betrusted-io/betrusted-hardware/mainboard-evt2/trusted_io_evt2.pdf

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
D | D
C | C
B | B
A | A

## Title

Size | Number | | Revision

A

Date: | 6/10/2019 | Sheet | of
File: | F:\largework\..\00_map.SchDoc | Drawn By:

# Licensed under CERN OHL v1.2 or later

# Copyright 2019 Andrew "bunnie" Huang

# Betrusted - Mainboard

Power sequencing:

* START with all systems off.
* VBUS (external power) applied, both U and T domains power on, and cannot be powered off until VBUS is removed. However, devices can still go into a power-saving mode on their own.
* VBUS removed:
* T-domain only powers down when both CPU and UP5K approve it. Normally, UP5K should cut its override once the CPU is confirmed to boot, so effectively the CPU has sef-control for power down.
* U-domain can self-power down whenever, but normally it's meant to be always-on. It powers off only when the battery reaches 0% to protect the battery. U-domain manages all charge and gas gauge hardware, and reports status to T-domain via COM SPI interface.
* It is up to the T-domain to monitor power via firmware COM SPI interface to UP5K to coordinate on the 0% power down. UP5K can trigger an interrupt in case of emergency, but T domain retains full authority to ignore it.
* Once U-domain is powered down, CPU can power on with T_TO_U_ON. This is useful in case RTC wakes up FPGA and it needs to also wake up the UP5K.

The nominal power strategy is power-on boot, and after a certain time-out interval of no activity, the FPGA will power itself down completely, and rely on the U-domain to monitor wake-up keys to power the FPGA domain up, or a callback can be set for a wake-up at no later than a specified timeout.

* U-domain can activate keyboard backlights to give instant UX response to monitor key press.
* T-domain can deny U-domain monitoring of keys via hardware signal, to avoid information leakage between the two domains.
* T-domain controls the LCD backlight, if present.
* After a T-domain power-down, the U-domain has the option to discharge the voltage rails with FPGA_DIS. This is provisioned to guarantee power sequencing is met even if the FPGA power down is very brief.

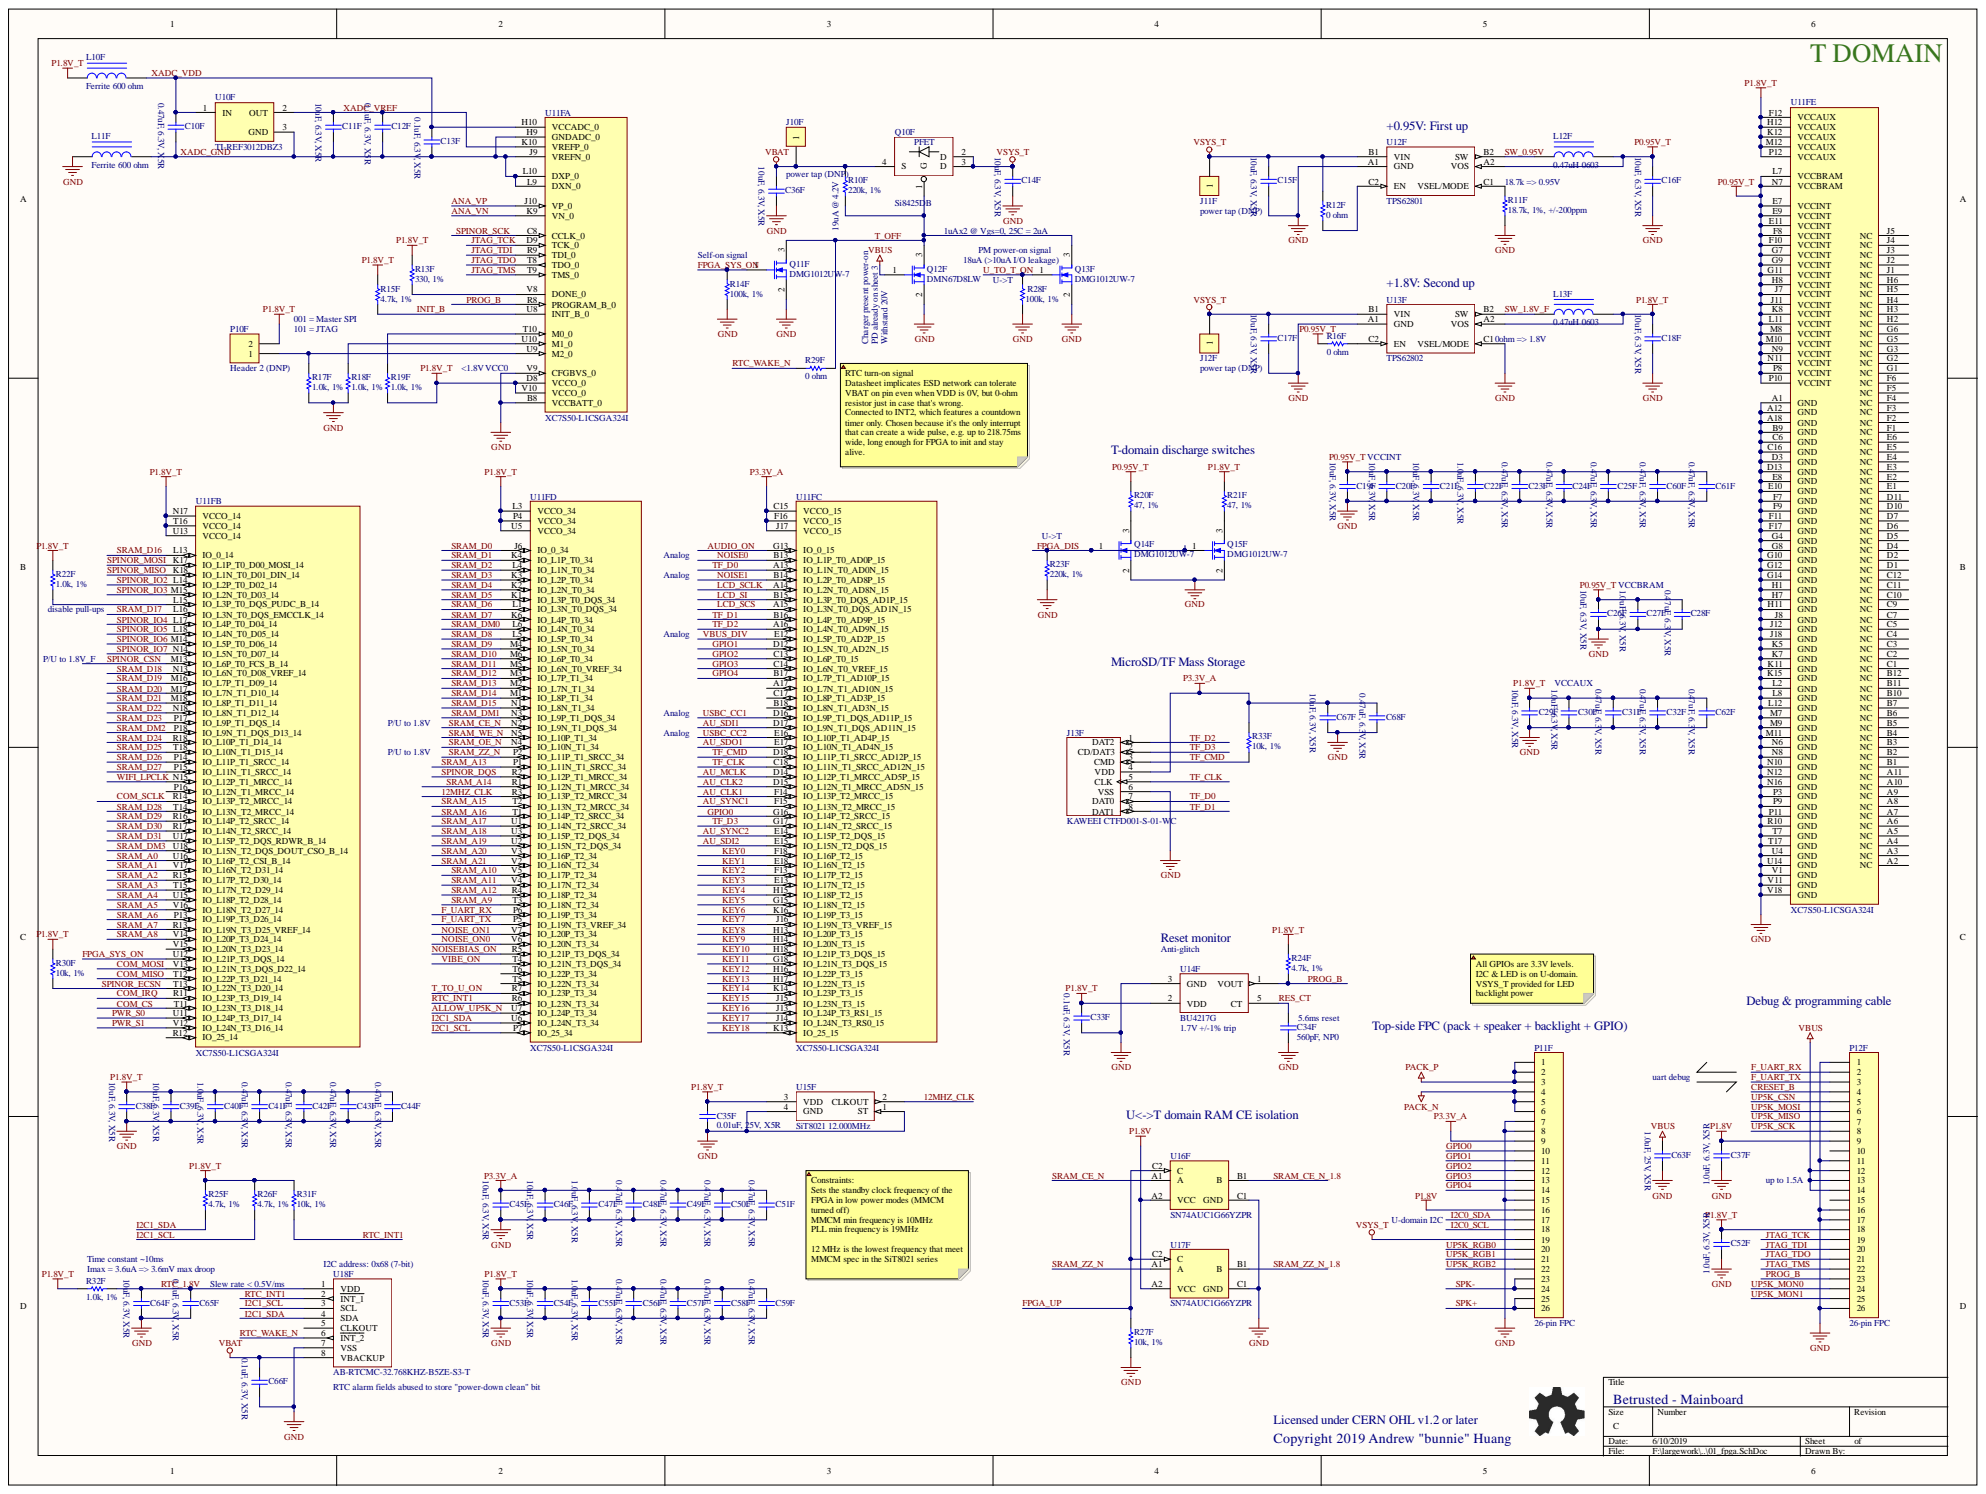
[picture p29: page 2]

Charger present power-on

PD already on sheet 3

RTC turn-on signal
Datasheet implicates ESD network can tolerate
VBAT on pin even when VDD is 0V, but 0-ohm
resistor just in case that's wrong.
Connected to INT2, which features a countdown
timer only. Chosen because it's the only interrupt
that can create a wide pulse, e.g. up to 218.75ms
wide, long enough for FPGA to init and stay
alive.

MicroSD/TF Mass Storage

Reset monitor Anti-glitch

All GPIOs are 3.3V levels.
I2C & LED is on U-domain.
VSYS_T provided for LED
backlight power

Top-side FPC (pack + speaker + backlight + GPIO)

U<->T domain RAM CE isolation

Constraints:
Sets the standby clock frequency of the
FPGA in low power modes (MMCM
turned off)
MMCM min frequency is 10MHz
PLL min frequency is 19MHz

12 MHz is the lowest frequency that meet
MMCM spec in the SiT8021 series

AB-RTCMC-32.768KHZ-B5ZE-S3-T
RTC alarm fields abused to store "power-down clean" bit

Licensed under CERN OHL v1.2 or later
Copyright 2019 Andrew "bunnie" Huang

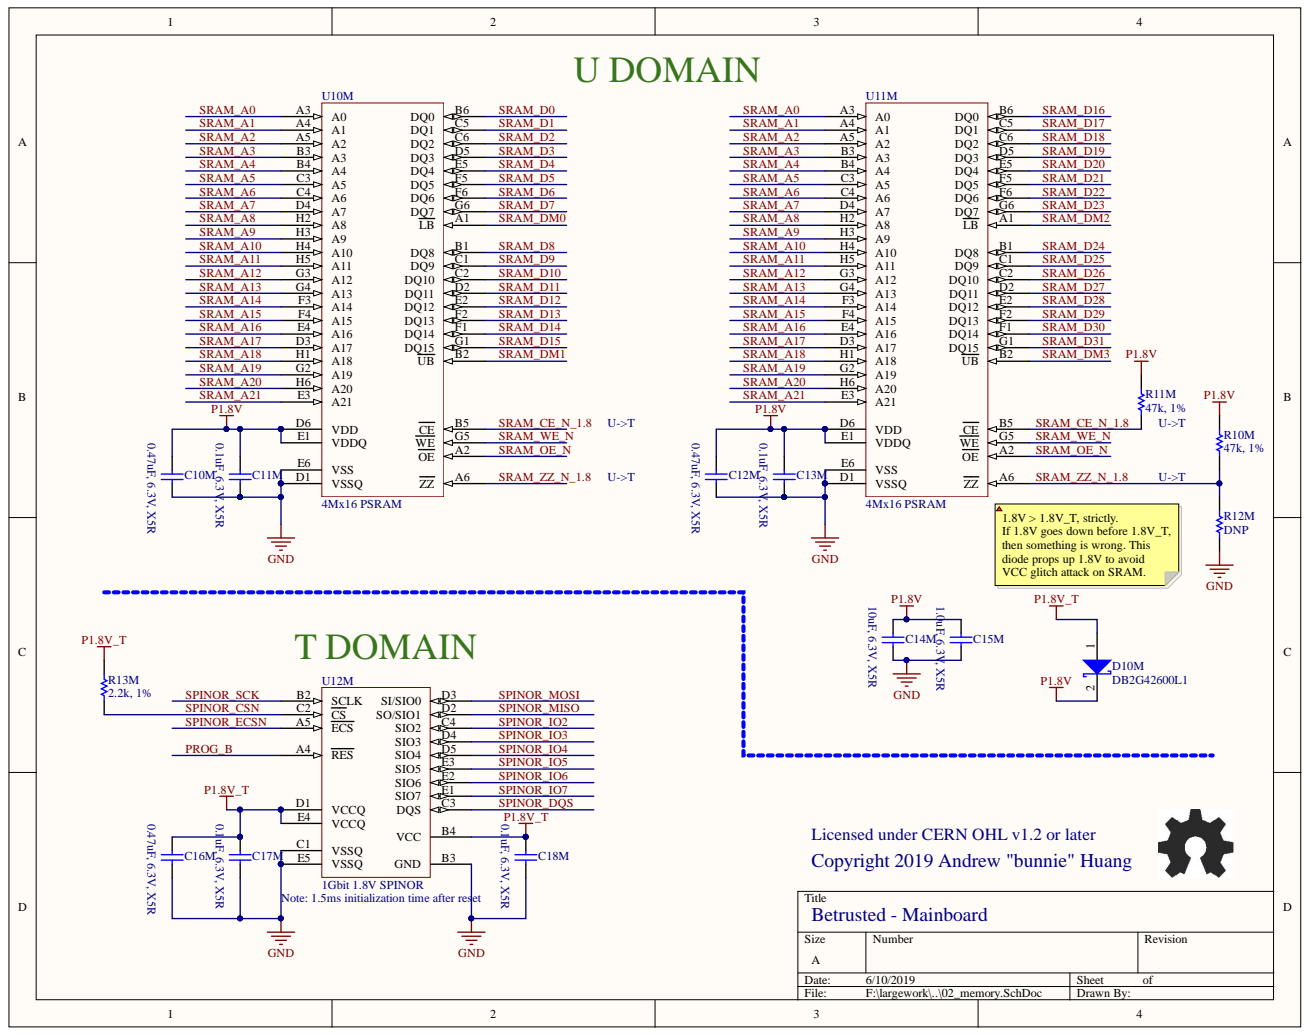
[picture p30: page 3]

Licensed under CERN
Copyright 2019 Andrew "bunnie" Huang

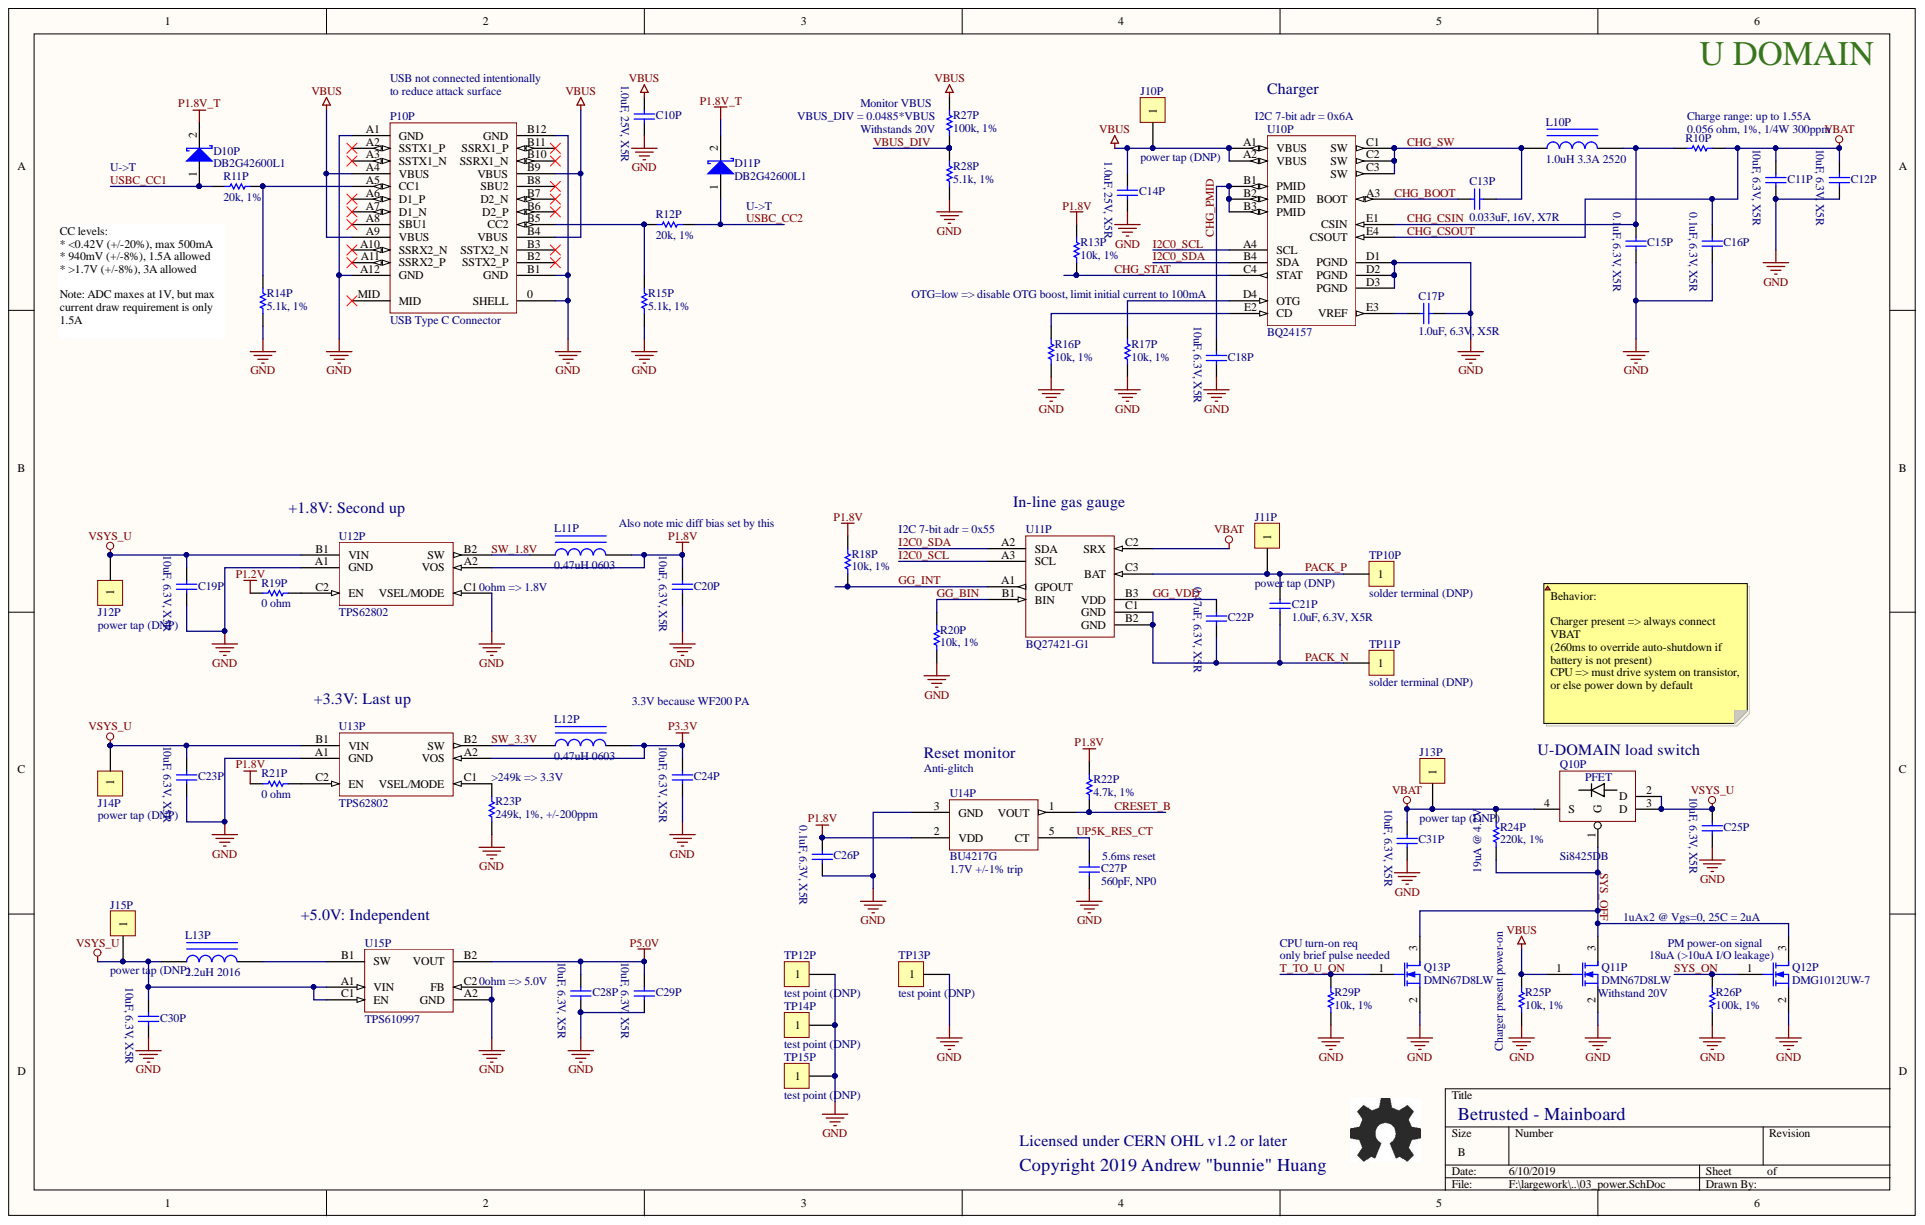
[picture p31: page 4]

USB not connected intentionally
to reduce attack surface

Charge range: up to 1.55A

Note: ADC maxes at 1V, but max
current draw requirement is only

OTG=low => disable OTG boost, limit initial current to 100mA

B | C18P solder terminal (DNP) | B

In-line gas gauge

Also note mic diff bias set by this

P1.2V 0 ohm | | EN C2 | L12P

BIN B1

Charger present => always connect
VBAT
(260ms to override auto-shutdown if
battery is not present)
CPU => must drive system on transistor,
or else power down by default

P1.8V 0 ohm | EN C2

PFET

power tap (DNP)

CPU turn-on req
only brief pulse needed

Charger present power-on

Licensed under CERN OHL v1.2 or later
Copyright 2019 Andrew "bunnie" Huang

Date: 6/10/2019 | Sheet of
File: F:\largework\..\03_power.SchDoc | Drawn By:

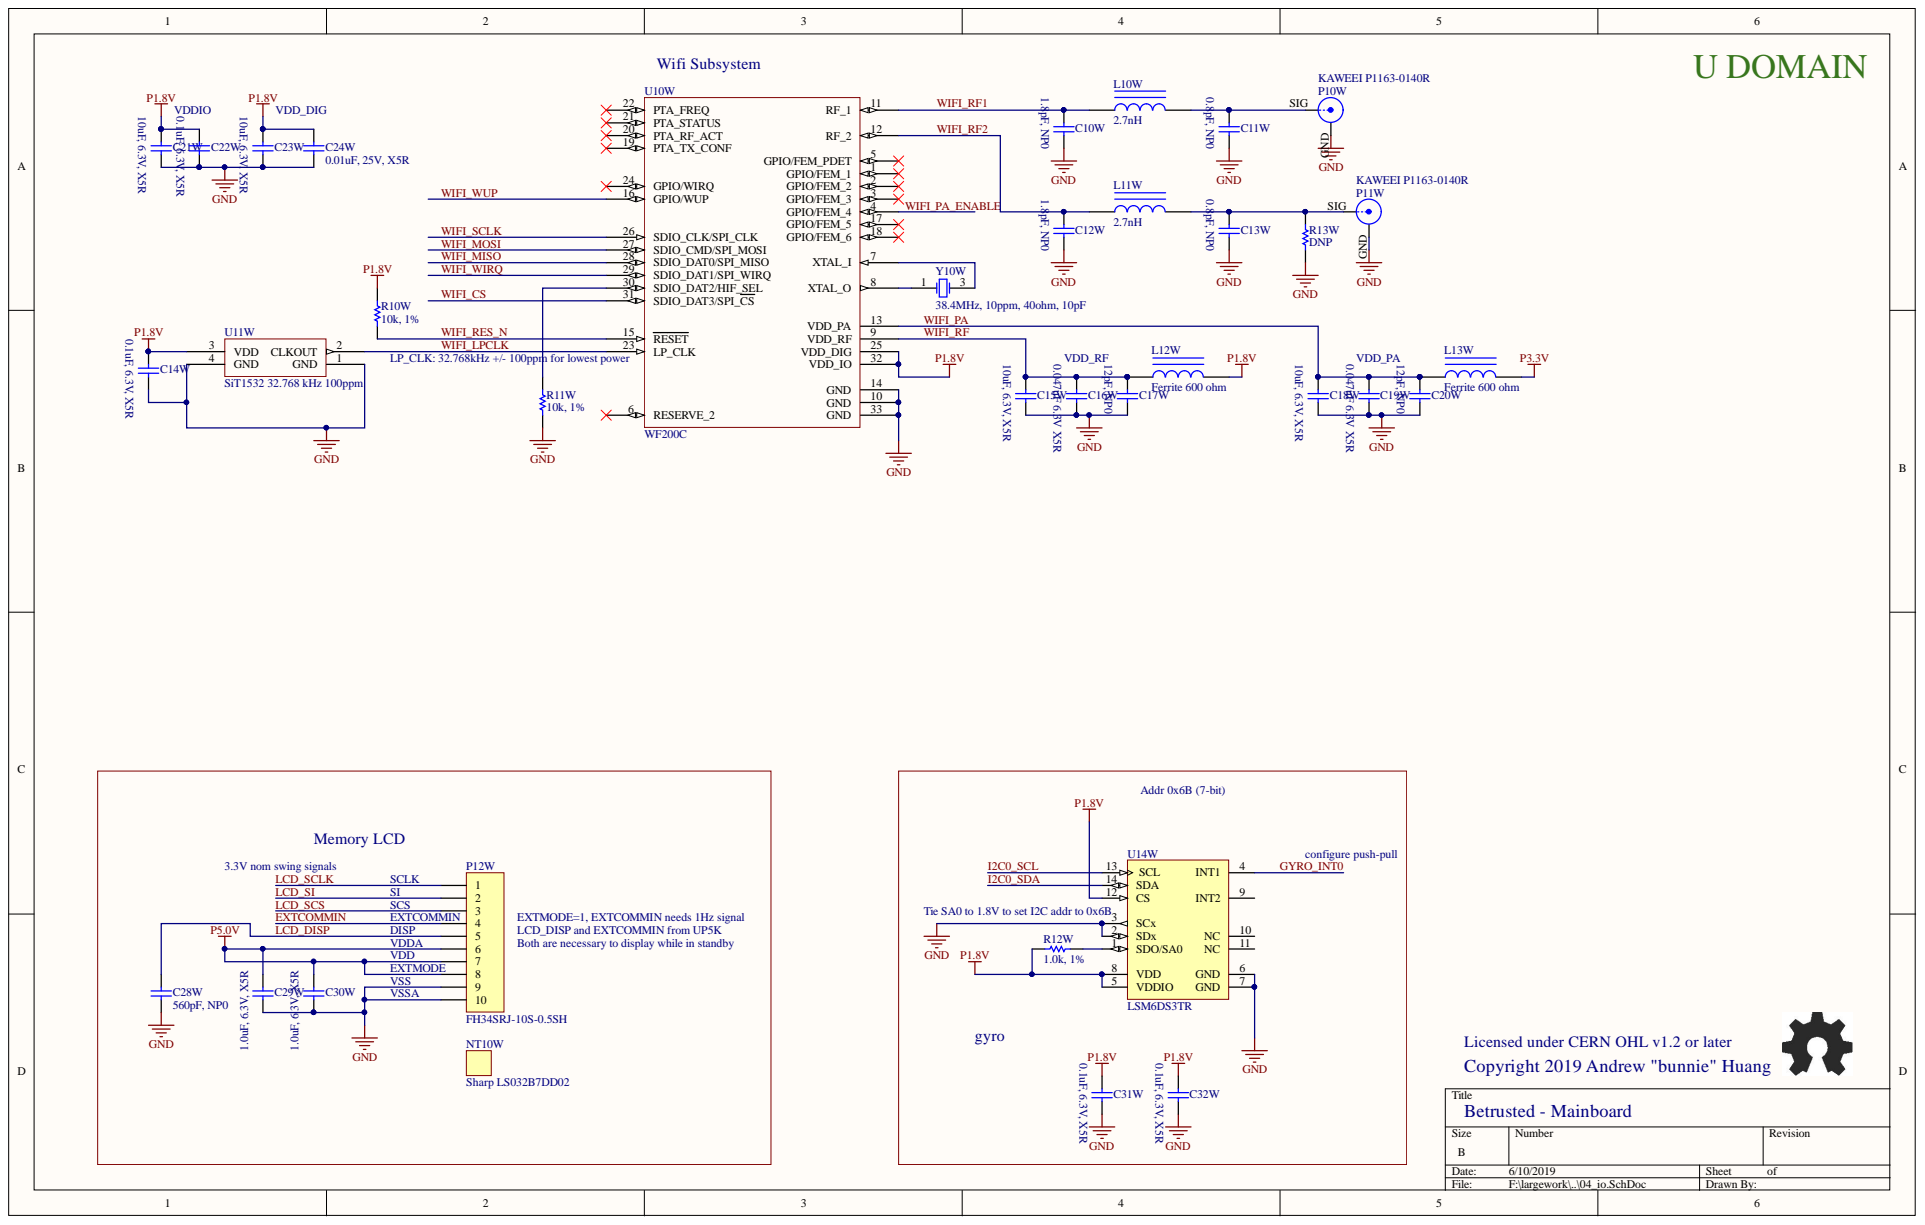
[picture p32: page 5]

Tie SA0 to 1.8V to set I2C addr to 0x6B

EXTMODE=1, EXTCOMMIN needs 1Hz signal
LCD_DISP and EXTCOMMIN from UP5K

VDD
EXTMODE
VSS

Licensed under CERN OHL v1.2 or later
Copyright 2019 Andrew "bunnie" Huang

Size B | Number | Revision

Date: 6/10/2019 | Sheet of
File: F:\largework\..\04_io.SchDoc | Drawn By:

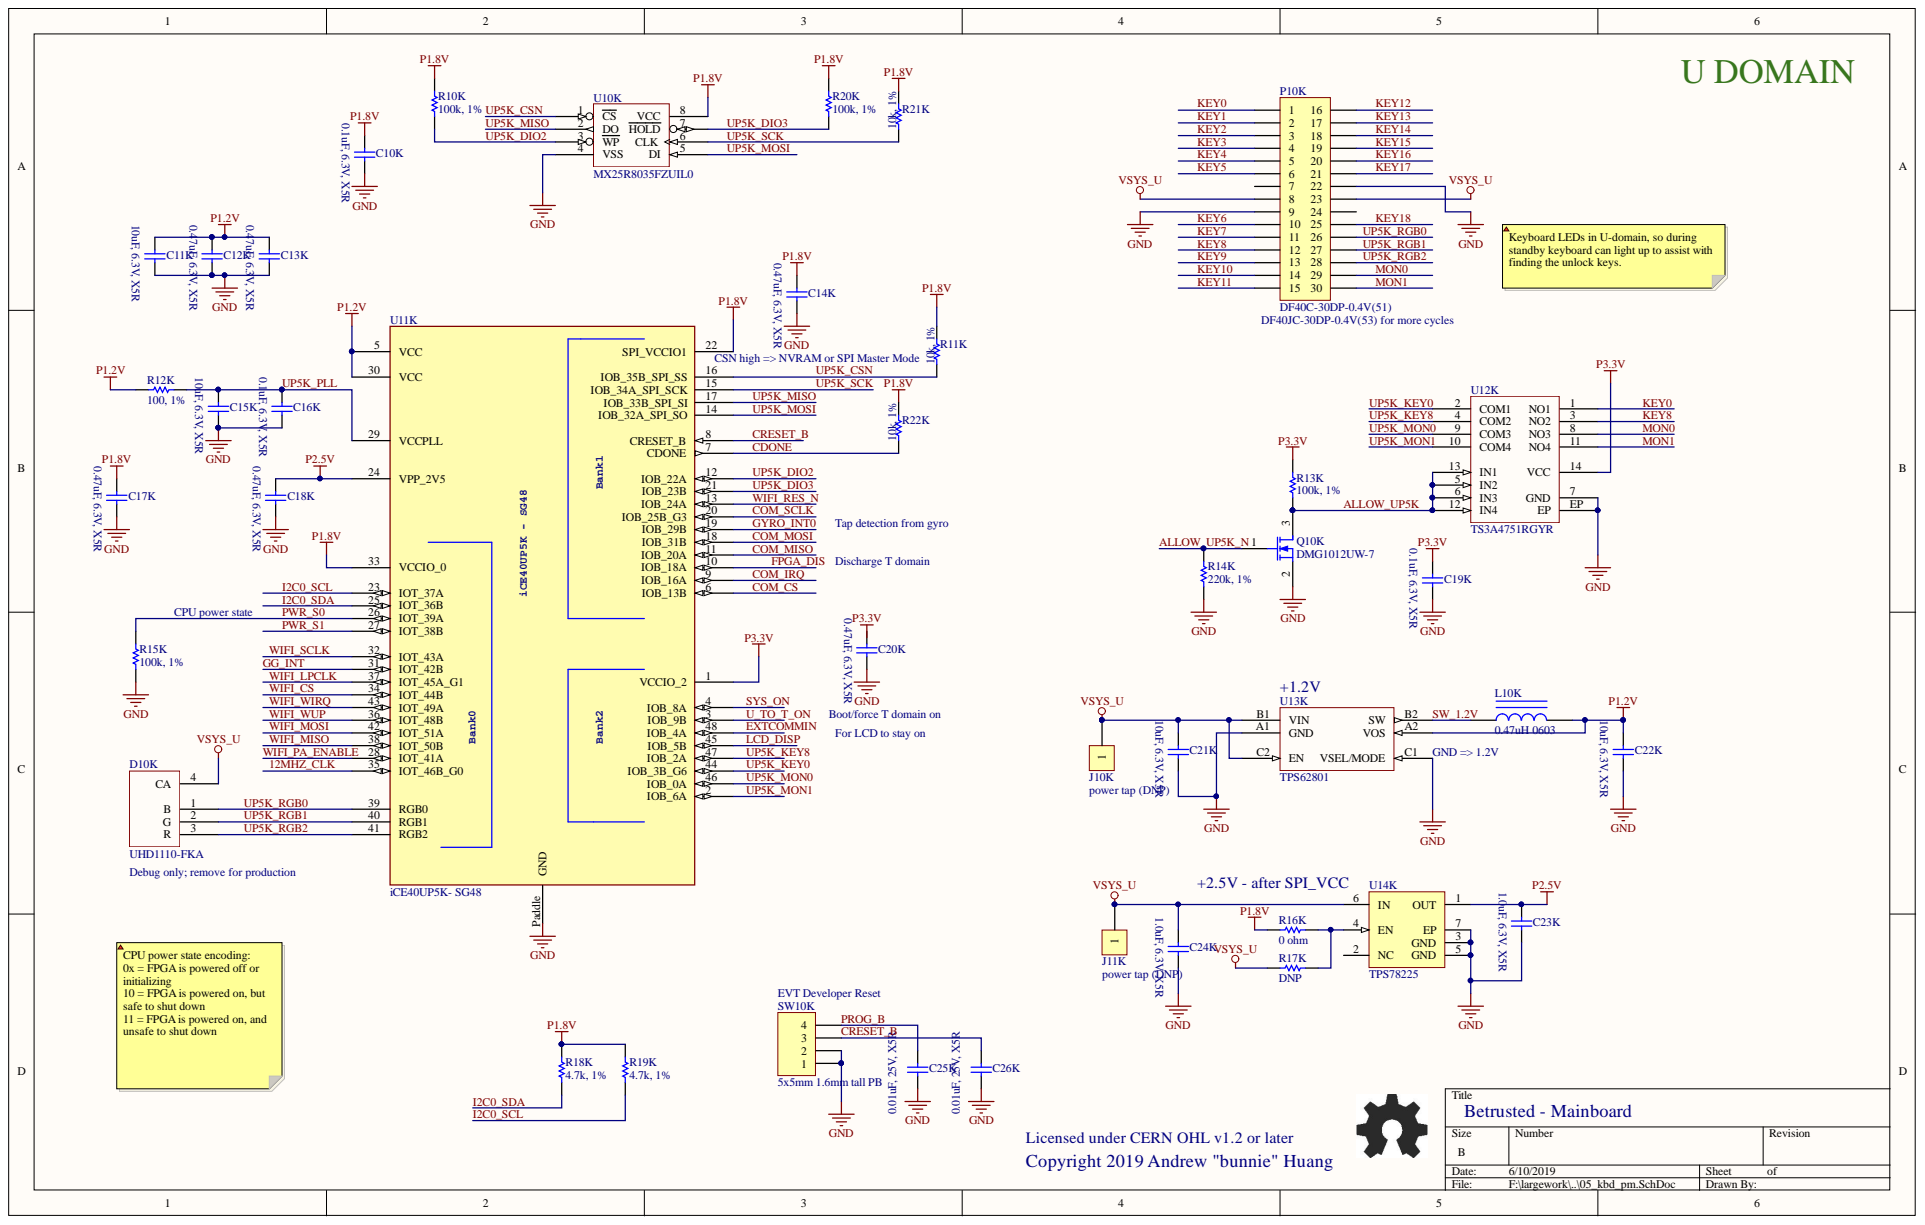
[picture p33: page 6]

Keyboard LEDs in U-domain, so during
standby keyboard can light up to assist with
finding the unlock keys.

CSN high => NVRAM or SPI Master Mode

Tap detection from gyro

Boot/force T domain on
For LCD to stay on

UHD1110-FKA
Debug only; remove for production

CPU power state encoding:
0x = FPGA is powered off or
initializing
10 = FPGA is powered on, but
safe to shut down
11 = FPGA is powered on, and
unsafe to shut down

Licensed under CERN OHL v1.2 or later
Copyright 2019 Andrew "bunnie" Huang

Date: 6/10/2019 | Sheet of
File: F:\largework\..\05_kbd_pm.SchDoc | Drawn By:

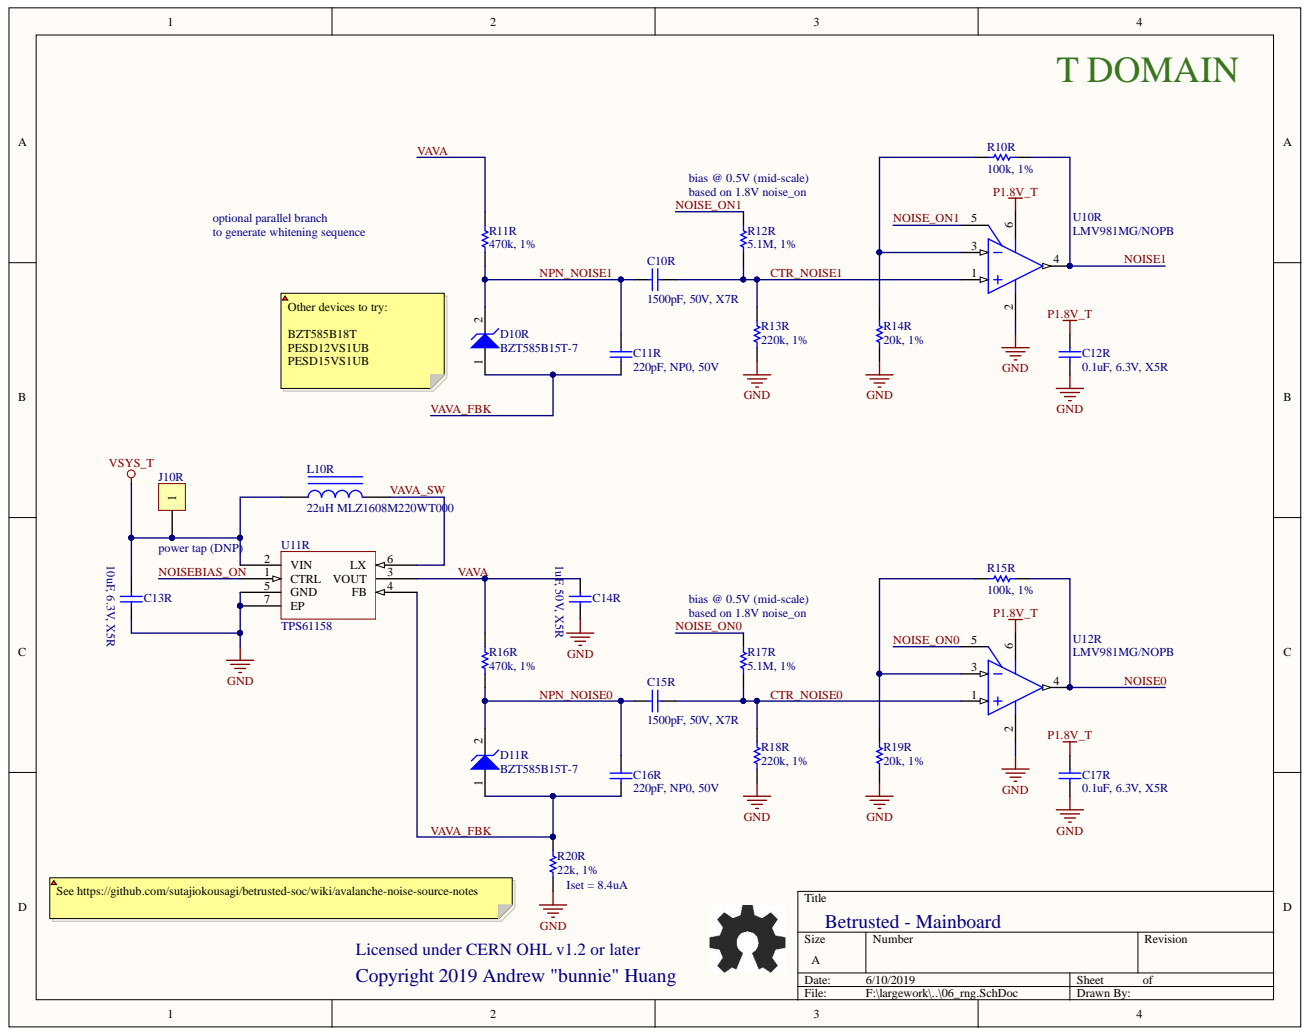
[picture p34: page 7]

optional parallel branch
to generate whitening sequence

Other devices to try:

See https://github.com/sutajiokousagi/betrusted-soc/wiki/avalanche-noise-source-notes

Licensed under CERN OHL v1.2 or later
Copyright 2019 Andrew "bunnie" Huang

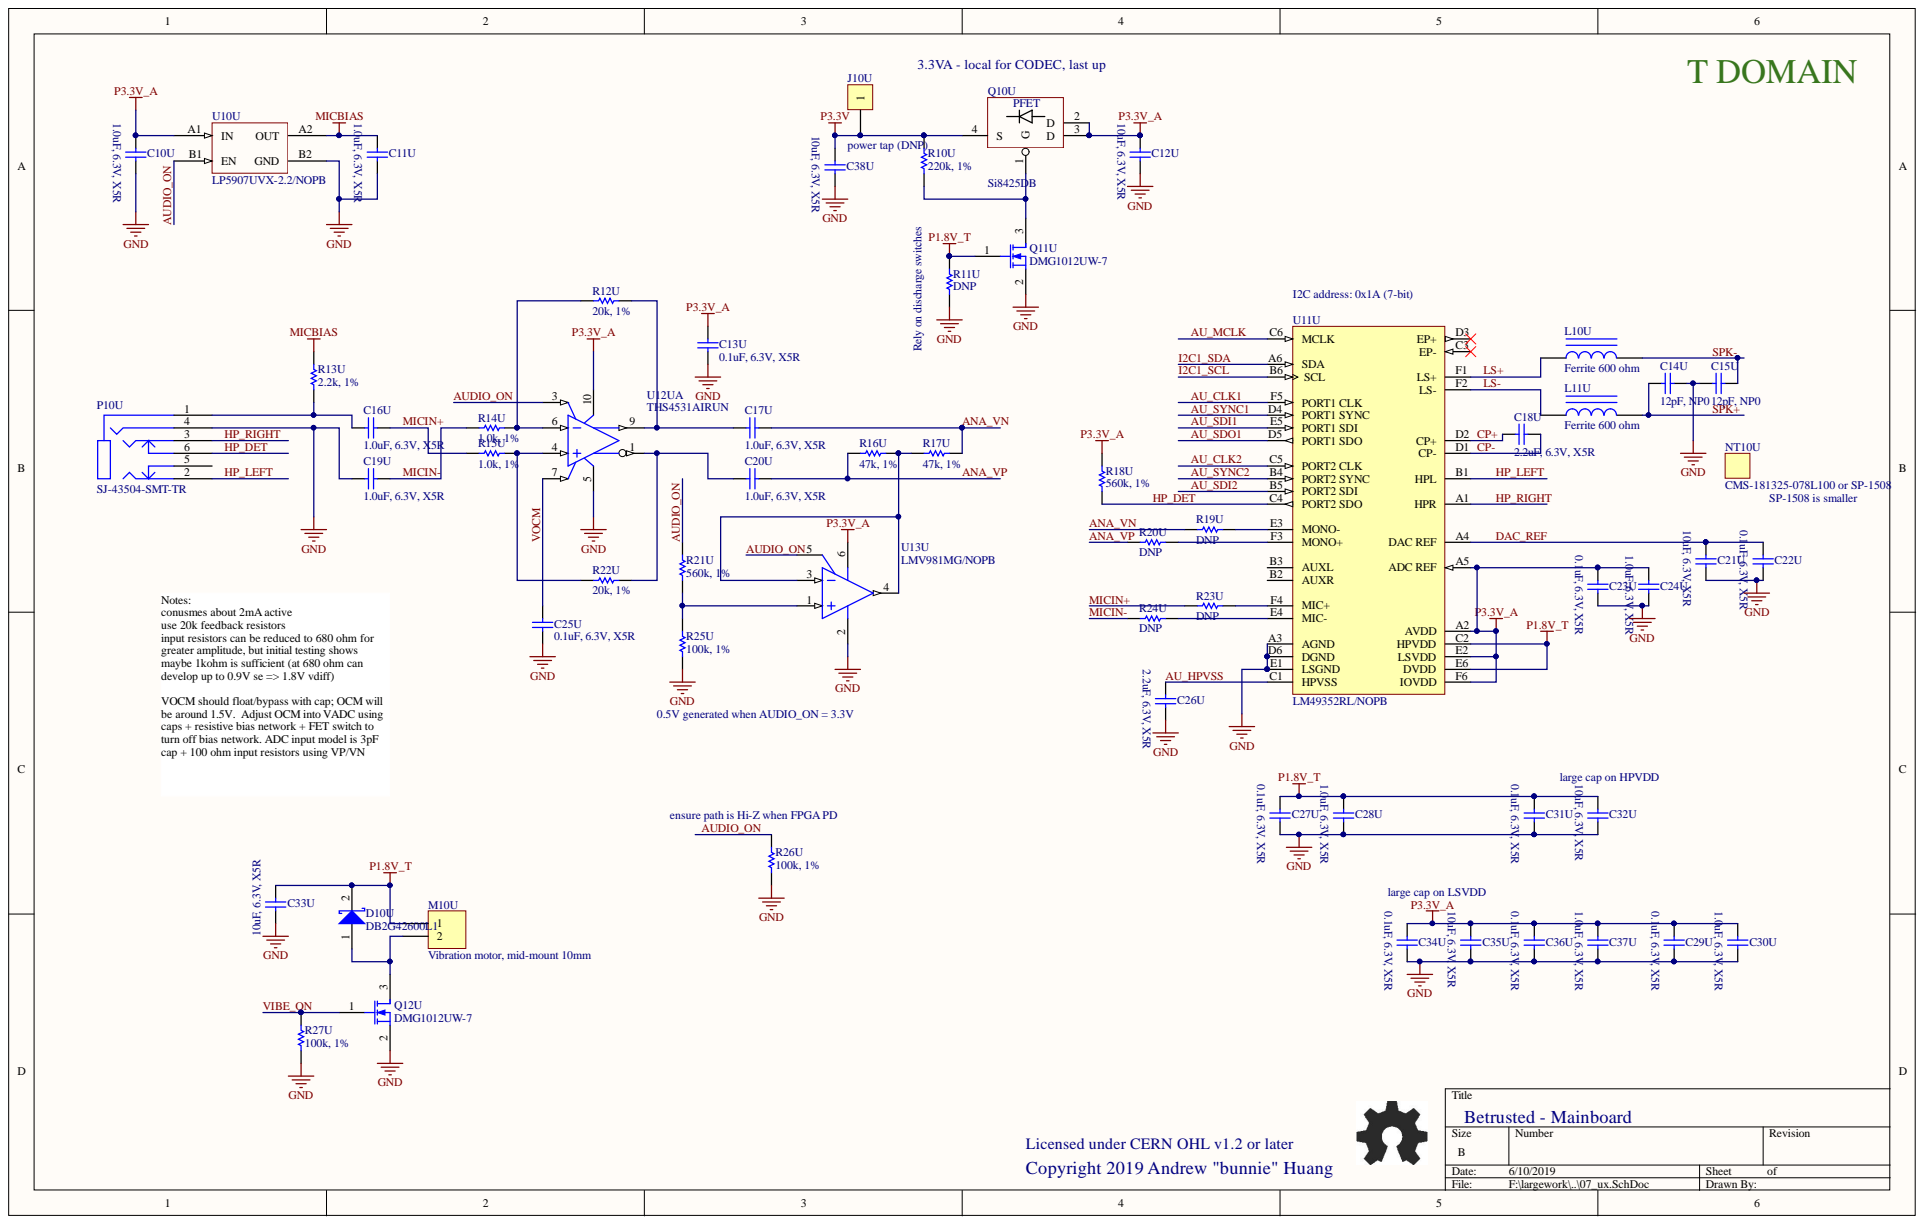
[picture p35: page 8]

3.3VA - local for CODEC, last up

PFET

10uF, 6.3V, X5R GND
GND Rely on discharge switches

power tap (DNP)

Notes:
conusmes about 2mA active
use 20k feedback resistors
input resistors can be reduced to 680 ohm for
greater amplitude, but initial testing shows
maybe 1kohm is sufficient (at 680 ohm can
develop up to 0.9V se => 1.8V vdiff)

VOCM should float/bypass with cap; OCM will
be around 1.5V. Adjust OCM into VADC using
caps + resistive bias network + FET switch to
turn off bias network. ADC input model is 3pF
cap + 100 ohm input resistors using VP/VN

large cap on HPVDD

ensure path is Hi-Z when FPGA PD
AUDIO_ON

large cap on LSVDD

D10U
DB2G42600L1

Licensed under CERN OHL v1.2 or later
Copyright 2019 Andrew "bunnie" Huang

Size B | Number | Revision

Date: 6/10/2019 | Sheet of
File: F:\largework\..\07_ux.SchDoc | Drawn By:
