betrusted-io/betrusted-hardware/kbd-v3/pcb/betrusted-kbd-v3.pdf

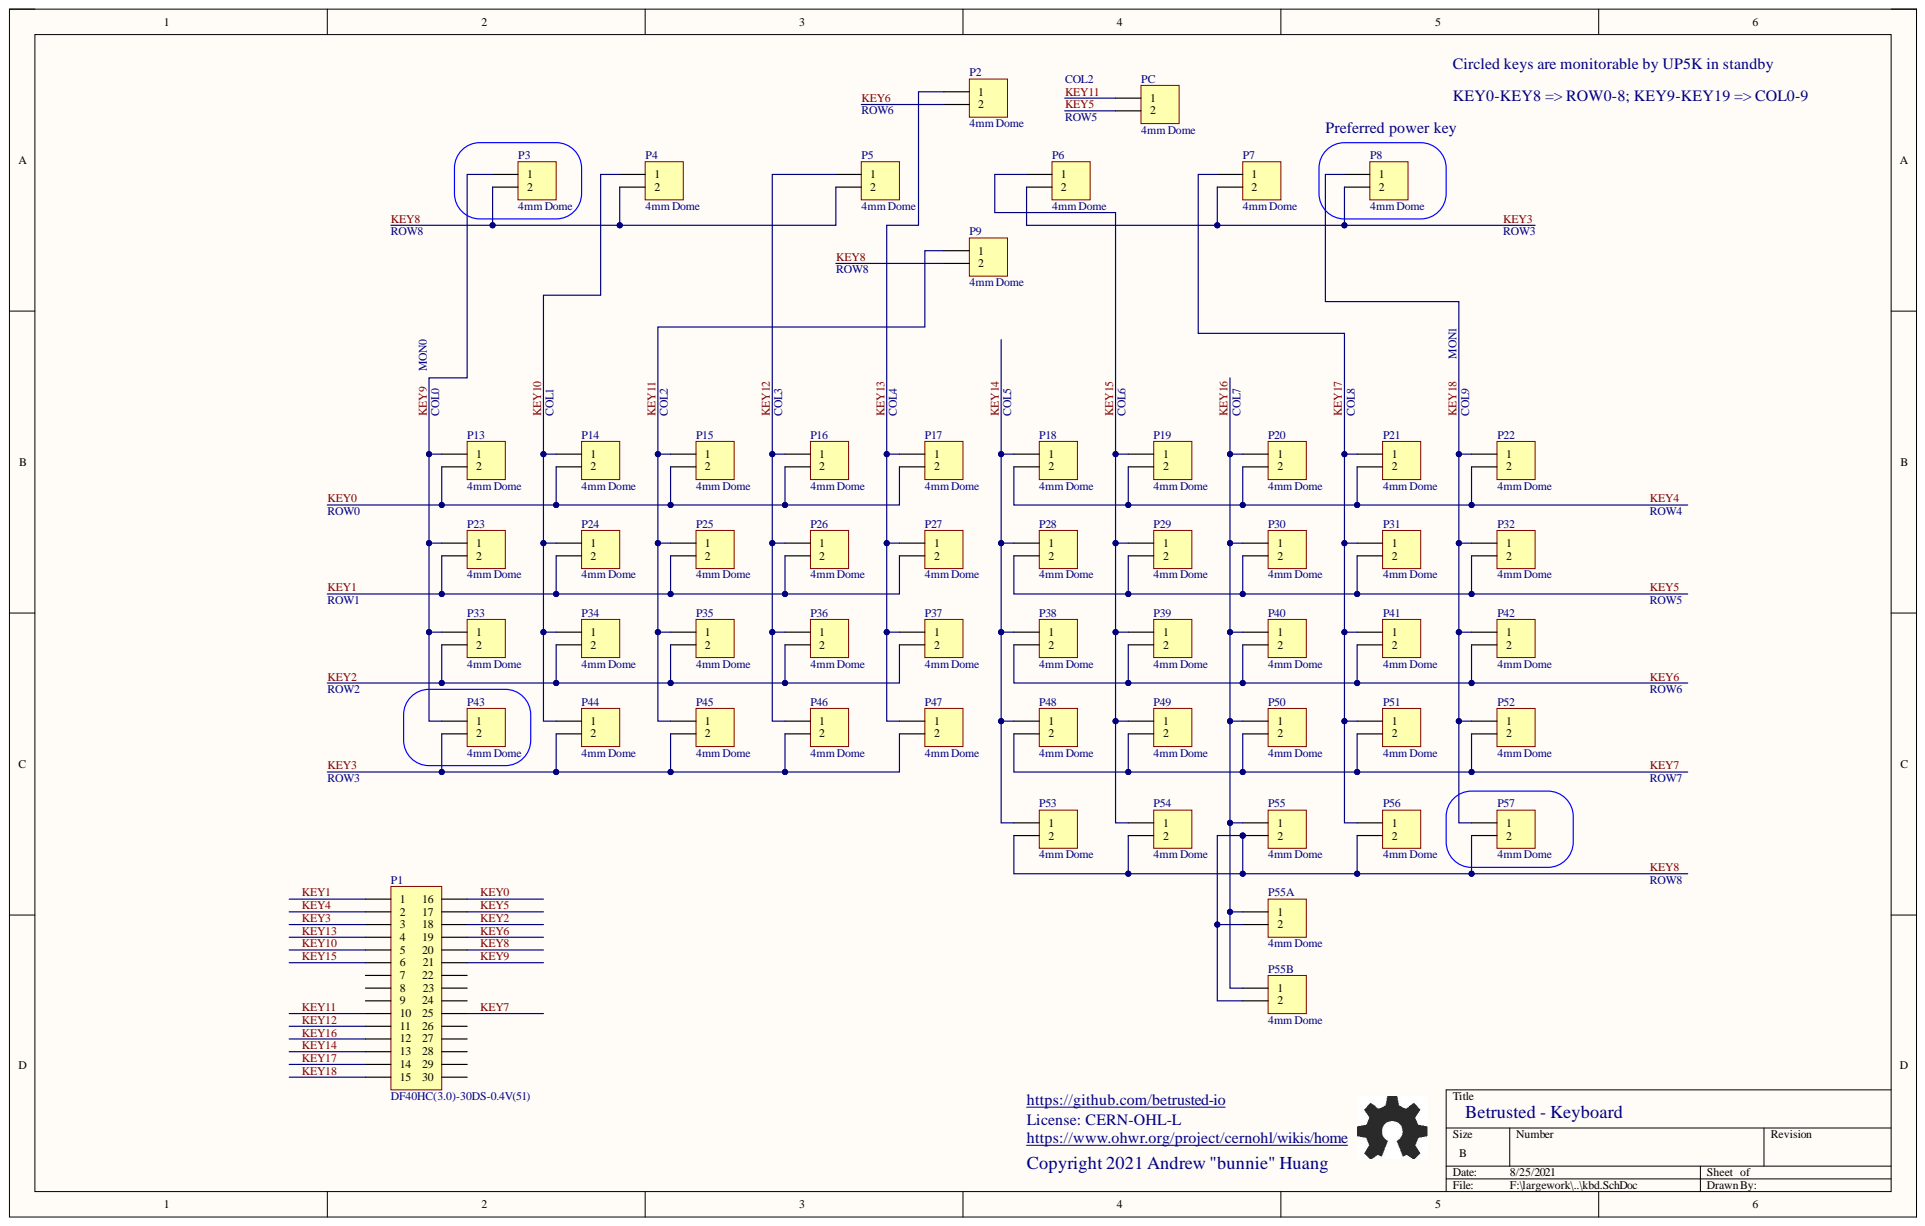
[picture p54: page 1]

MON1 Circled keys are monitorable by UP5K in standby

https://github.com/betrusted-io
License: CERN-OHL-L
https://www.ohwr.org/project/cernohl/wikis/home
Copyright 2021 Andrew "bunnie" Huang

Size B | Number | Revision

Date: 8/25/2021 | Sheet of
File: F:\largework\..\kbd.SchDoc | Drawn By:
