betrusted-io/betrusted-hardware/case-v1/betrusted-dvt1-fpc-dims.PDF

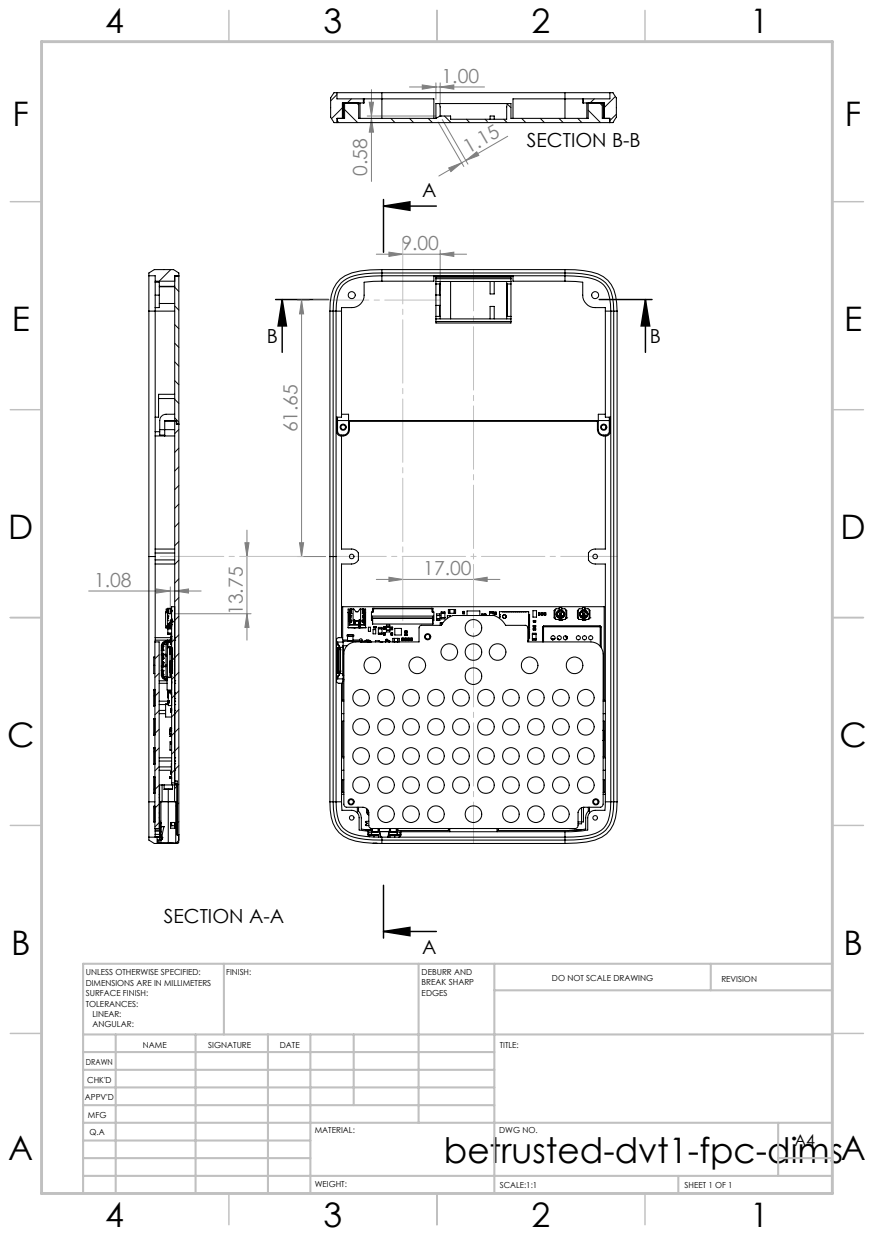
[picture p55: page 1]
SECTION A-A; SECTION B-B; FINISH:; DEBURR AND; BREAK SHARP; DO NOT SCALE DRAWING; REVISION; SCALE:1:1; SHEET 1 OF 1

UNLESS OTHERWISE SPECIFIED:
DIMENSIONS ARE IN MILLIMETERS
SURFACE FINISH:
TOLERANCES:
LINEAR:
ANGULAR:

NAME | SIGNATURE | DATE | | | | TITLE:

DRAWN
CHK'D
APPV'D
MFG
Q.A | | | | MATERIAL: | DWG NO. | A4

betrusted-dvt1-fpc-dims
