betrusted-io/betrusted-hardware/case-v1/t-domain-shield.PDF

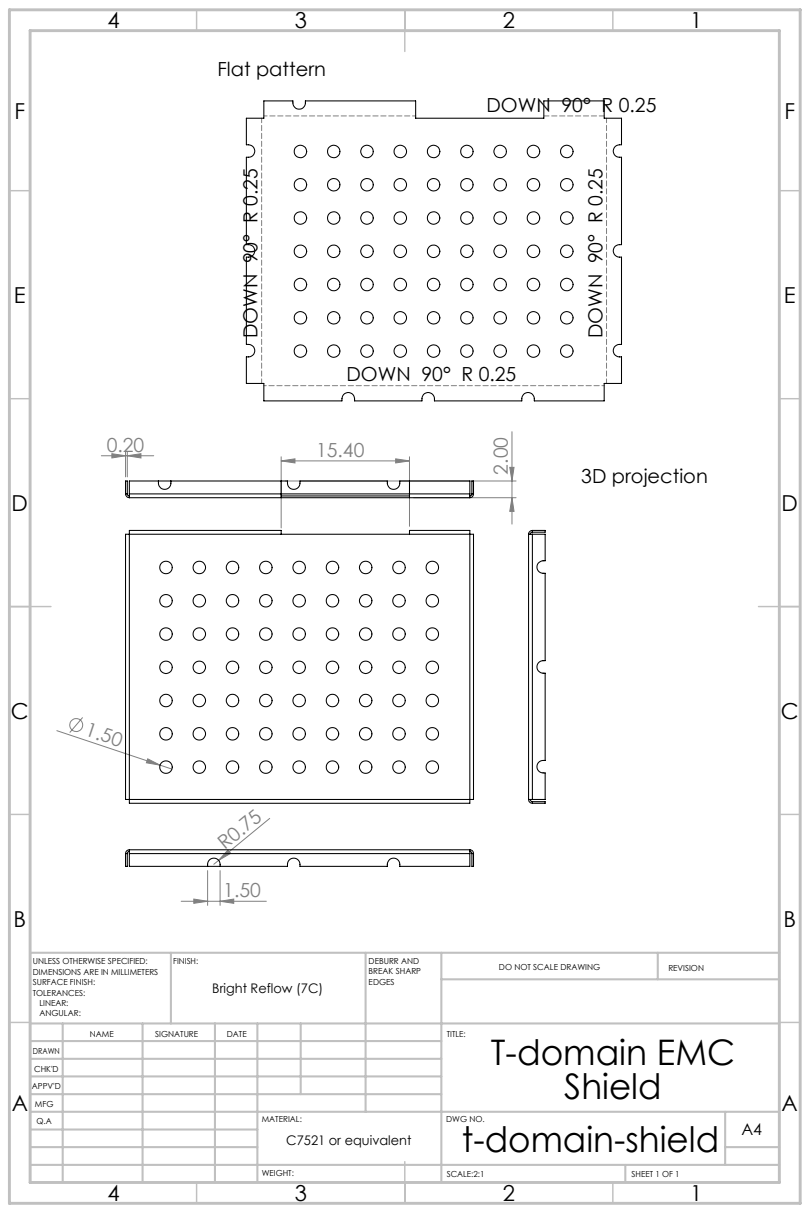
[picture p56: page 1]
DOWN 90° R 0.25; 3D projection; FINISH:; DEBURR AND; BREAK SHARP; DO NOT SCALE DRAWING; REVISION; SCALE:2:1; SHEET 1 OF 1; Bright Reflow (7C)

Flat pattern | DOWN 90° R 0.25

UNLESS OTHERWISE SPECIFIED:
DIMENSIONS ARE IN MILLIMETERS
SURFACE FINISH:
TOLERANCES:
LINEAR:
ANGULAR:

NAME | SIGNATURE | DATE | | | | TITLE: T-domain EMC Shield

DRAWN
CHK'D
APPV'D
MFG
Q.A | | | | MATERIAL: | DWG NO. t-domain-shield | A4 C7521 or equivalent
