betrusted-io/betrusted-hardware/case-v1/fab/bottom-case.PDF

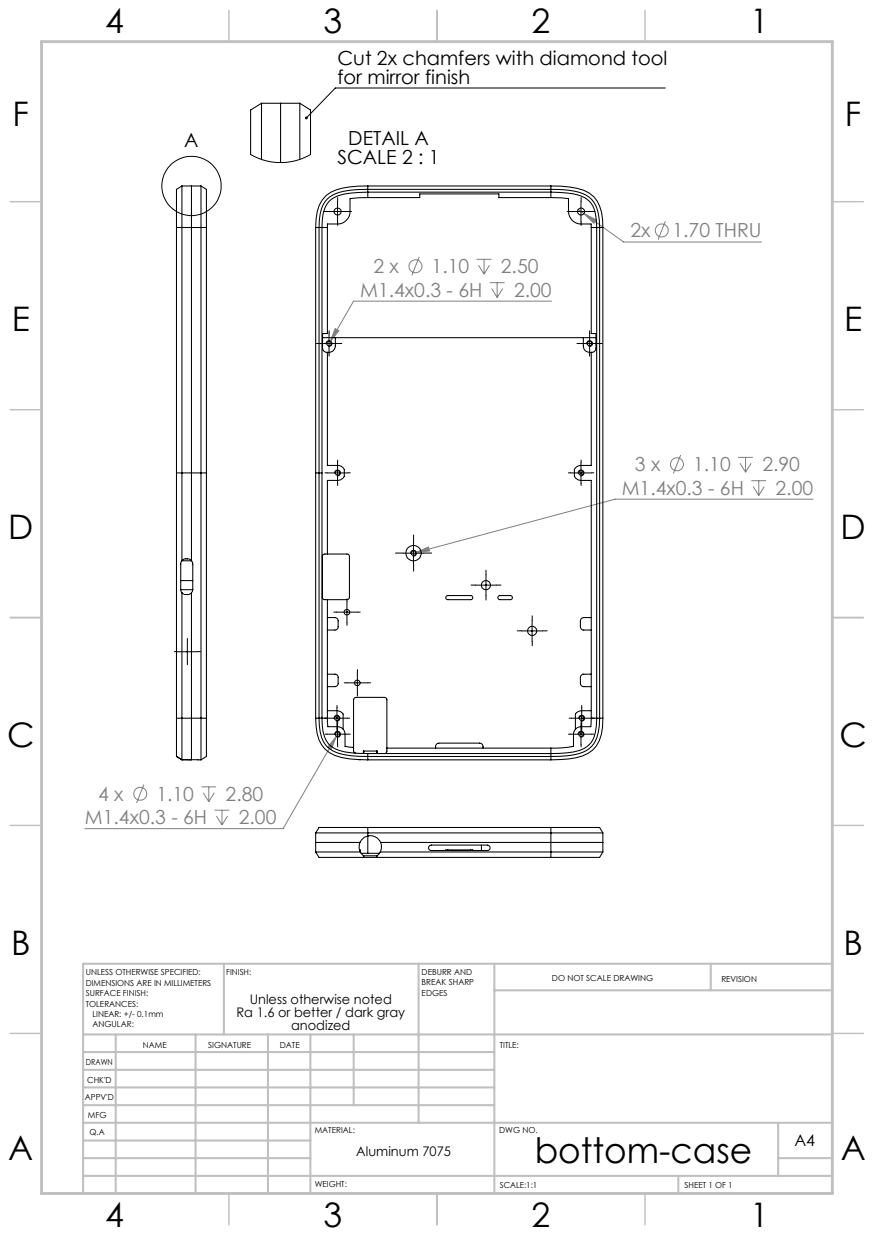
[picture p57: page 1]
2x 1.70 THRU; DETAIL A; SCALE 2 : 1; FINISH:; DEBURR AND; BREAK SHARP; DO NOT SCALE DRAWING; REVISION; SCALE:1:1; SHEET 1 OF 1

Cut 2x chamfers with diamond tool
for mirror finish

UNLESS OTHERWISE SPECIFIED:
DIMENSIONS ARE IN MILLIMETERS
SURFACE FINISH:
TOLERANCES:
LINEAR: +/- 0.1mm
ANGULAR:

Unless otherwise noted
Ra 1.6 or better / dark gray
anodized

NAME | SIGNATURE | DATE | | | | TITLE:

DRAWN
CHK'D
APPV'D
MFG
Q.A | | | | MATERIAL: | DWG NO. bottom-case | A4 Aluminum 7075
