betrusted-io/betrusted-hardware/case-v1/fab/radome.PDF

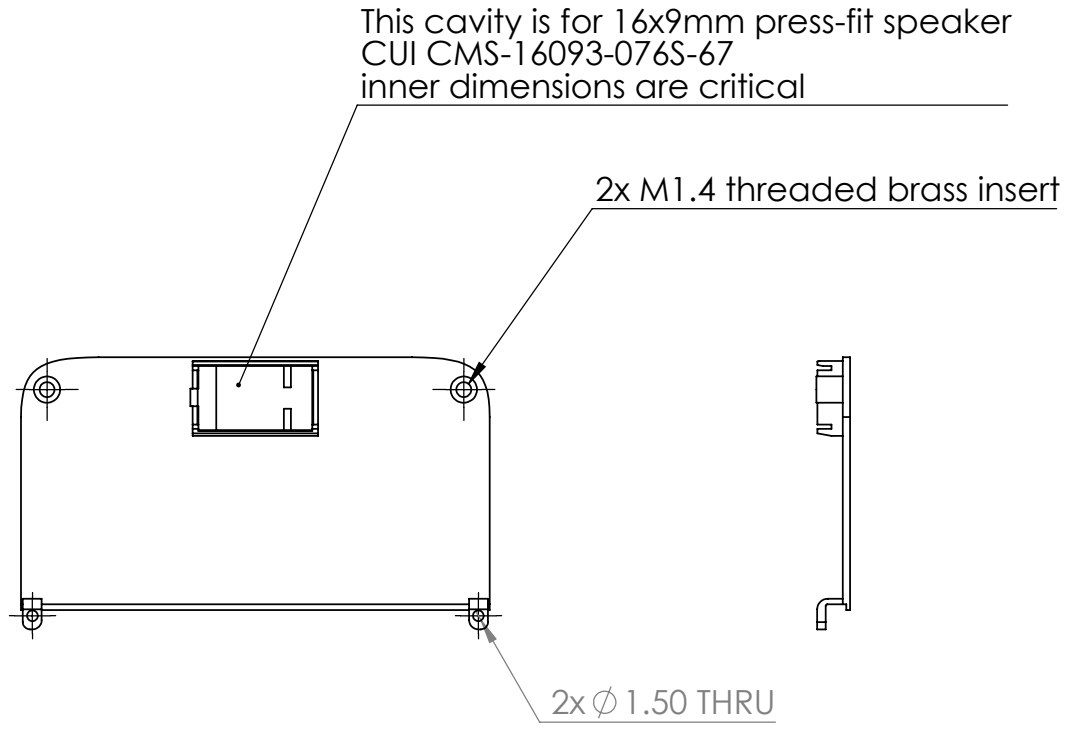
[picture p58: page 1]
2x 1.50 THRU; FINISH:; DEBURR AND; BREAK SHARP; DO NOT SCALE DRAWING; REVISION; SCALE:1:1; SHEET 1 OF 1

This cavity is for 16x9mm press-fit speaker
CUI CMS-16093-076S-67
inner dimensions are critical

2x M1.4 threaded brass insert

UNLESS OTHERWISE SPECIFIED:
DIMENSIONS ARE IN MILLIMETERS
SURFACE FINISH:
TOLERANCES:
LINEAR:
ANGULAR:

Fine satin black

NAME | SIGNATURE | DATE | | | | TITLE:

DRAWN
CHK'D
APPV'D
MFG
Q.A | | | | MATERIAL: ABS/PC | DWG NO. radome | A4
