betrusted-io/betrusted-hardware/rpi-hat-v3/Assembly Drawings.pdf

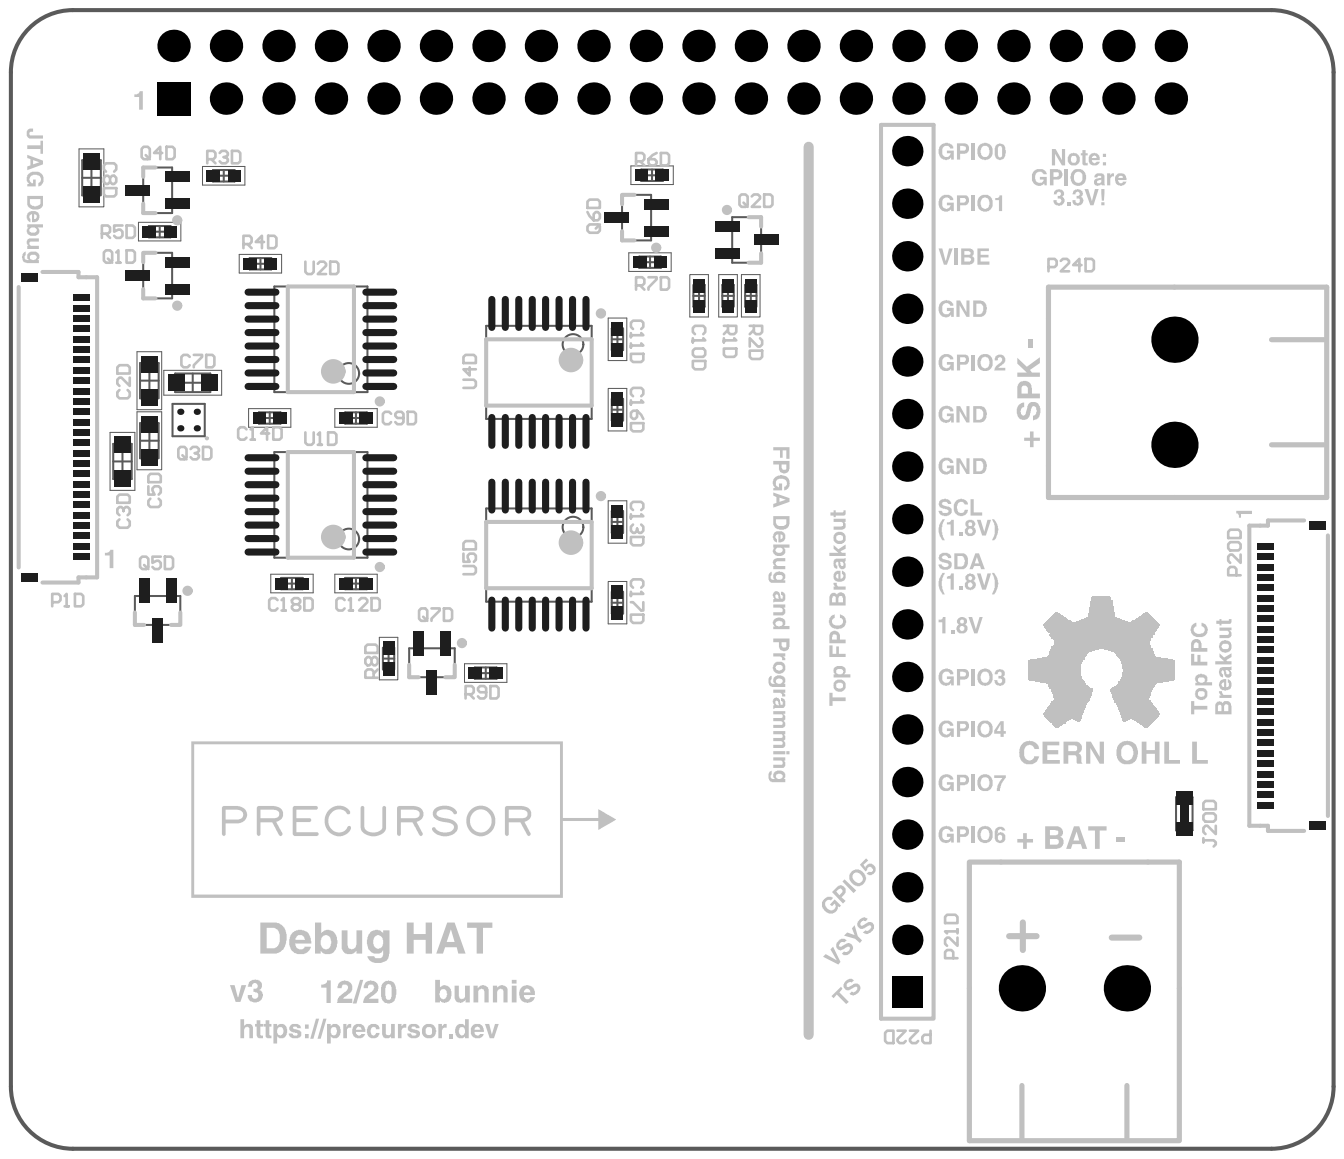
[picture p59: page 1]

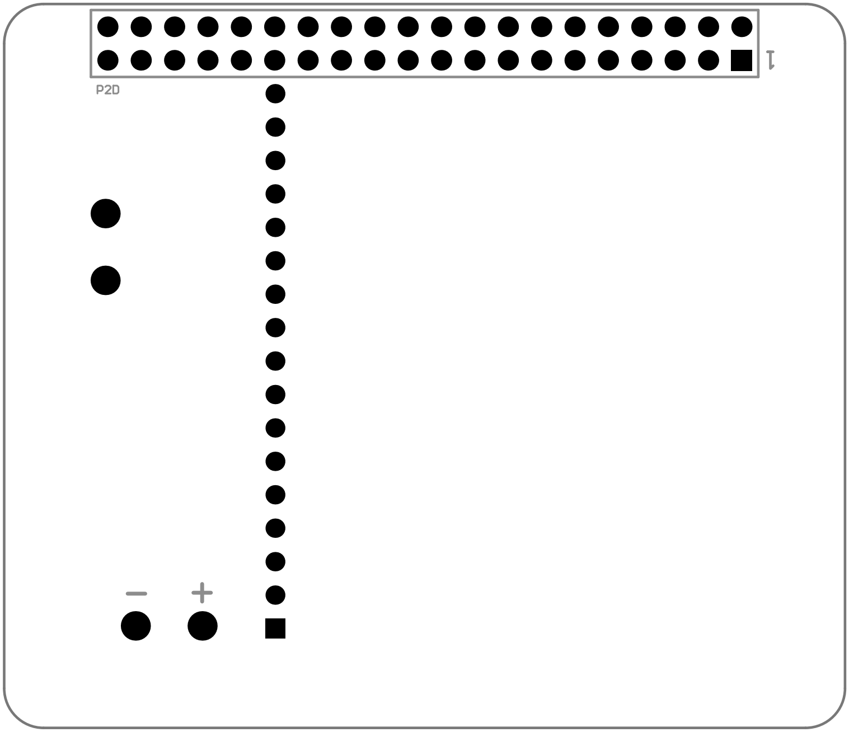
[picture p60: figure]
