betrusted-io/betrusted-hardware/case-v1/dvt1-test-mb.PDF

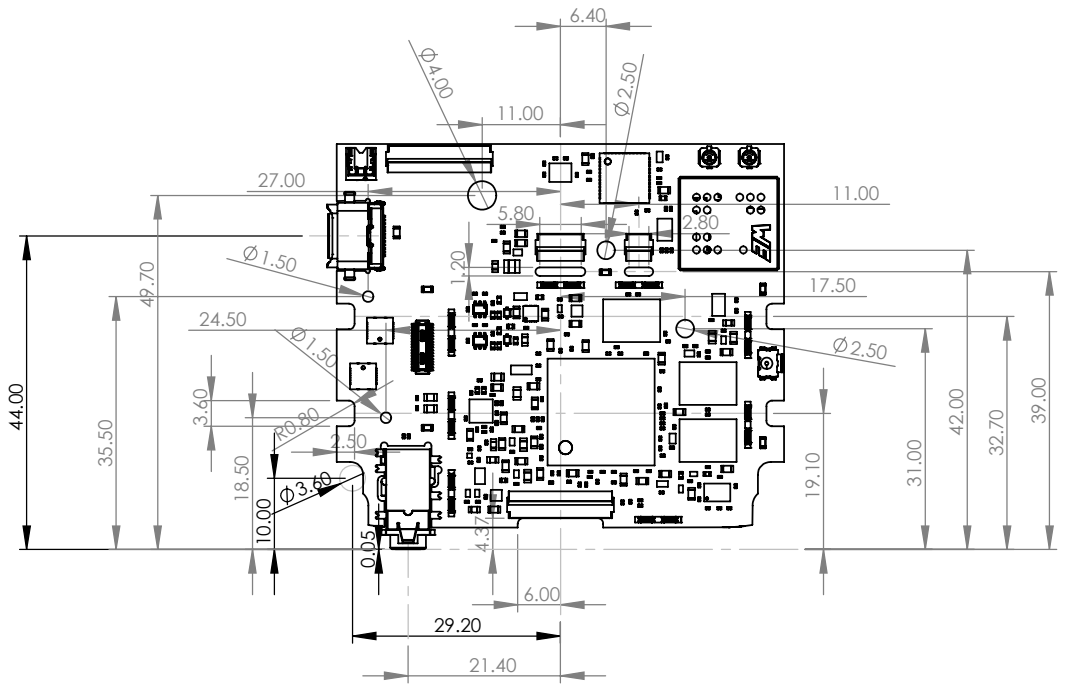
[picture p61: page 1]
