betrusted-io/betrusted-hardware/kbd-v2/betrusted-kbd-v2.pdf

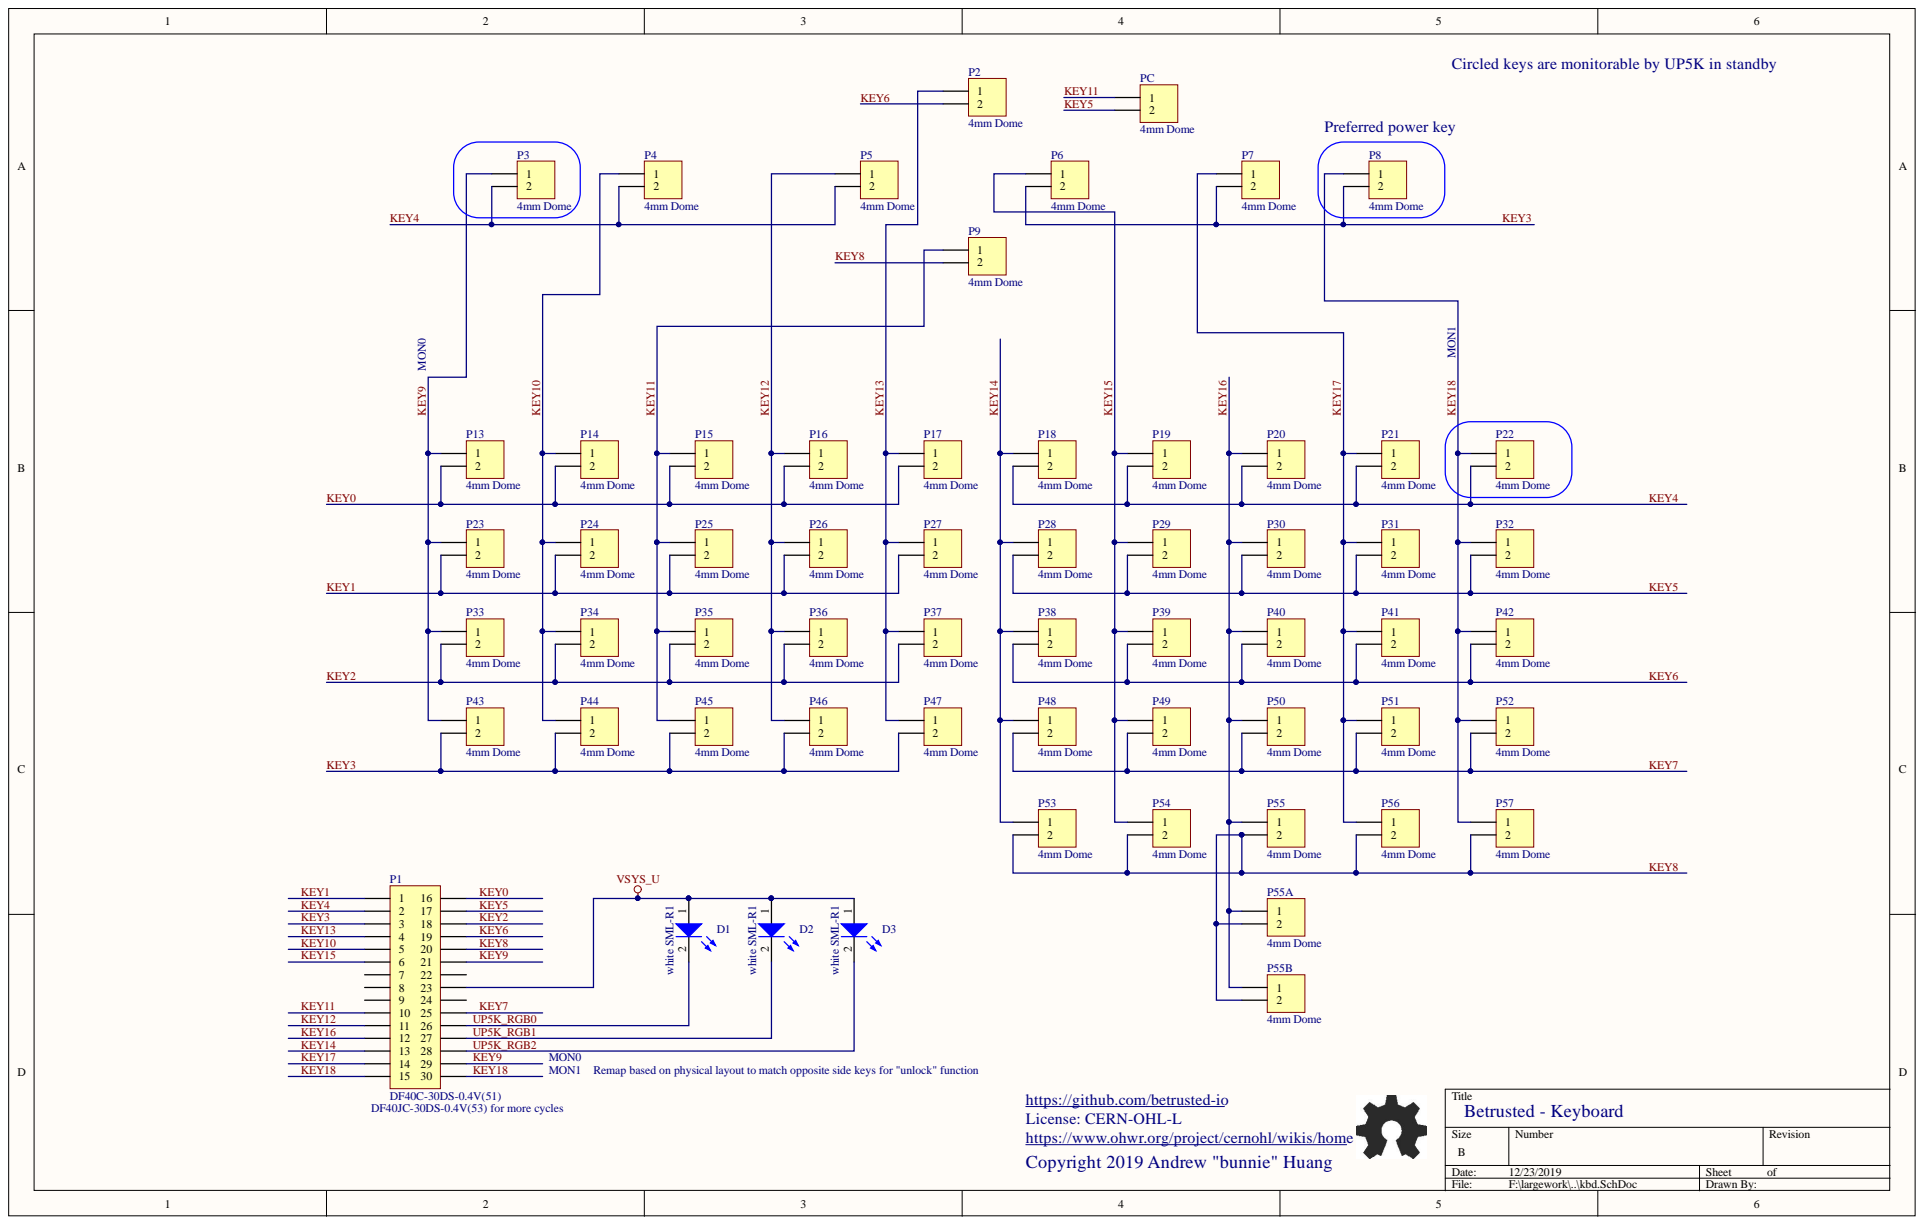
[picture p62: page 1]

MON1 Circled keys are monitorable by UP5K in standby

Remap based on physical layout to match opposite side keys for "unlock" function

https://github.com/betrusted-io
License: CERN-OHL-L
https://www.ohwr.org/project/cernohl/wikis/home
Copyright 2019 Andrew "bunnie" Huang

Size B | Number | Revision

Date: 12/23/2019 | Sheet of
File: F:\largework\..\kbd.SchDoc | Drawn By:

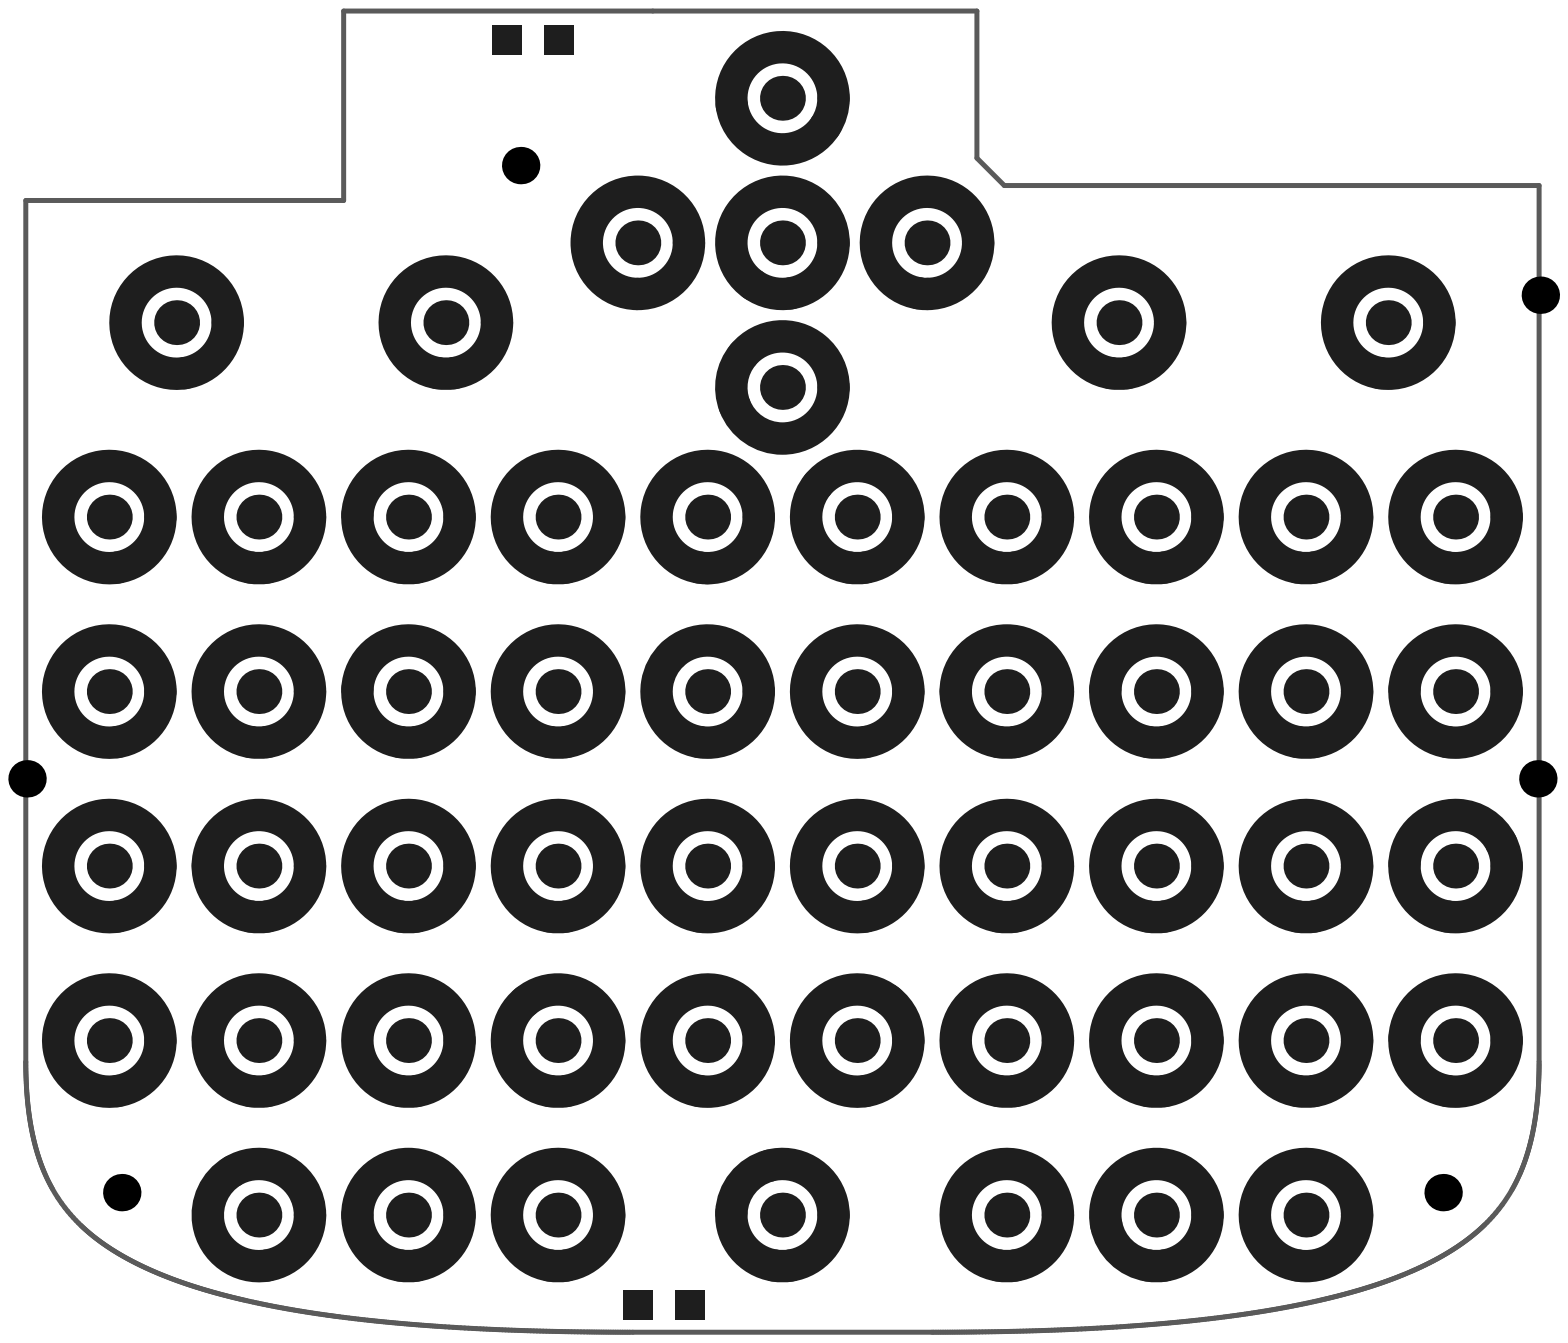
[picture p63: page 2]
